Mateusz-alicante/Praxis3-PB/1. Design Process Artifacts/Pictures/Prototyping/Initial_Box_Design.webp

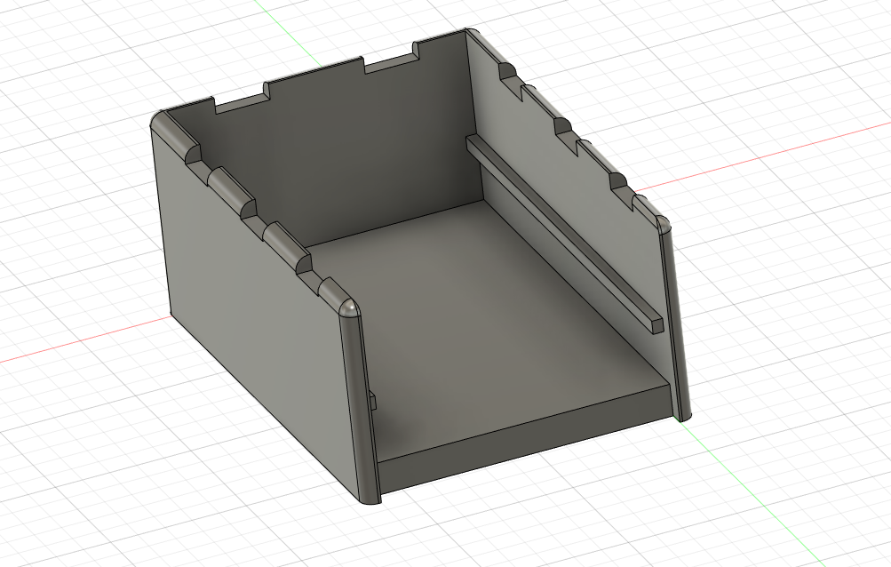
1. Design Process Artifacts/Pictures/Prototyping/Initial_Box_Design.webp
