Mateusz-alicante/Praxis3-PB/1. Design Process Artifacts/Pictures/Prototyping/Initial_Button_CAD.png

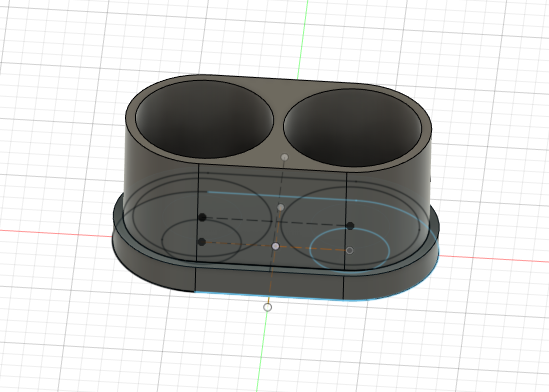
1. Design Process Artifacts/Pictures/Prototyping/Initial_Button_CAD.png
