Mateusz-alicante/Praxis3-PB/1. Design Process Artifacts/Pictures/Prototyping/Initial_Circuit_Diagram.webp

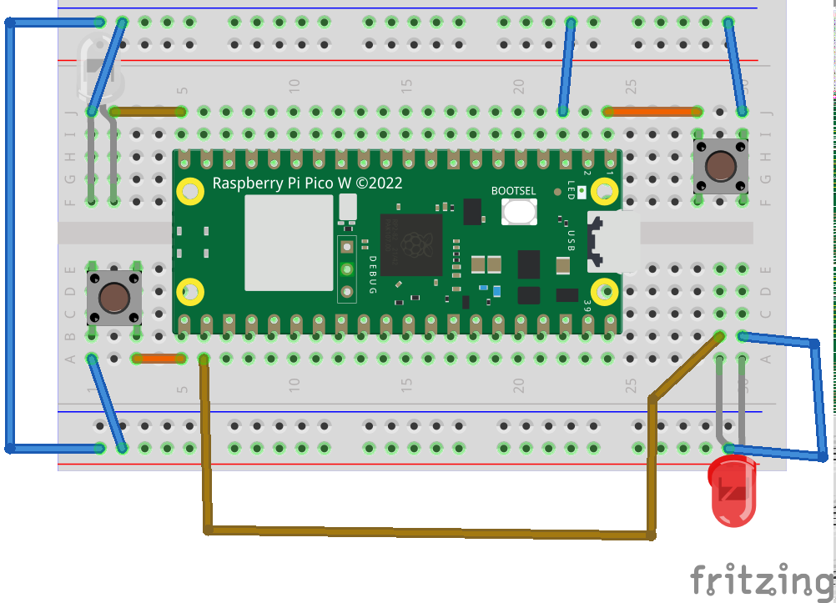
1. Design Process Artifacts/Pictures/Prototyping/Initial_Circuit_Diagram.webp
