Mateusz-alicante/Praxis3-PB/1. Design Process Artifacts/Pictures/Prototyping/Initial_Integration_Idea.webp

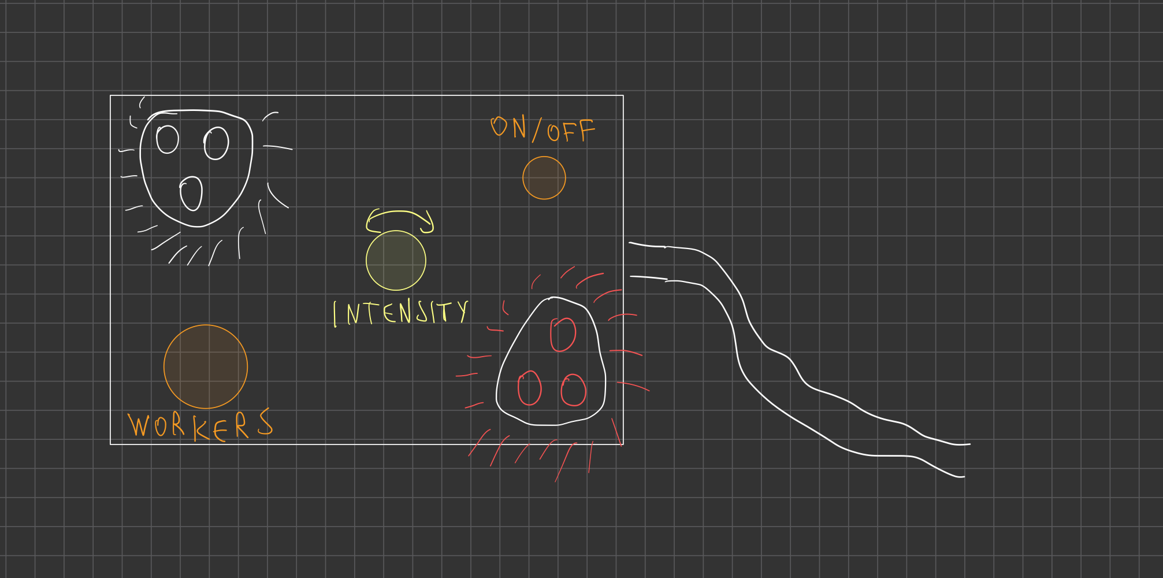
1. Design Process Artifacts/Pictures/Prototyping/Initial_Integration_Idea.webp
