Mateusz-alicante/Praxis3-PB/2. Final Design Artifacts/Final_CAD_CAM/Pictures/Section_View_2.png

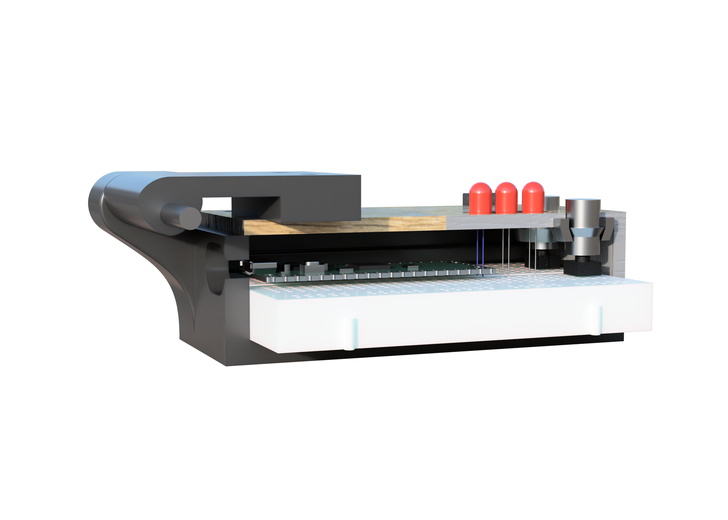
2. Final Design Artifacts/Final_CAD_CAM/Pictures/Section_View_2.png
