Mateusz-alicante/Praxis3-PB/2. Final Design Artifacts/Final_Hardware/Final_Circuit_Diagram.png

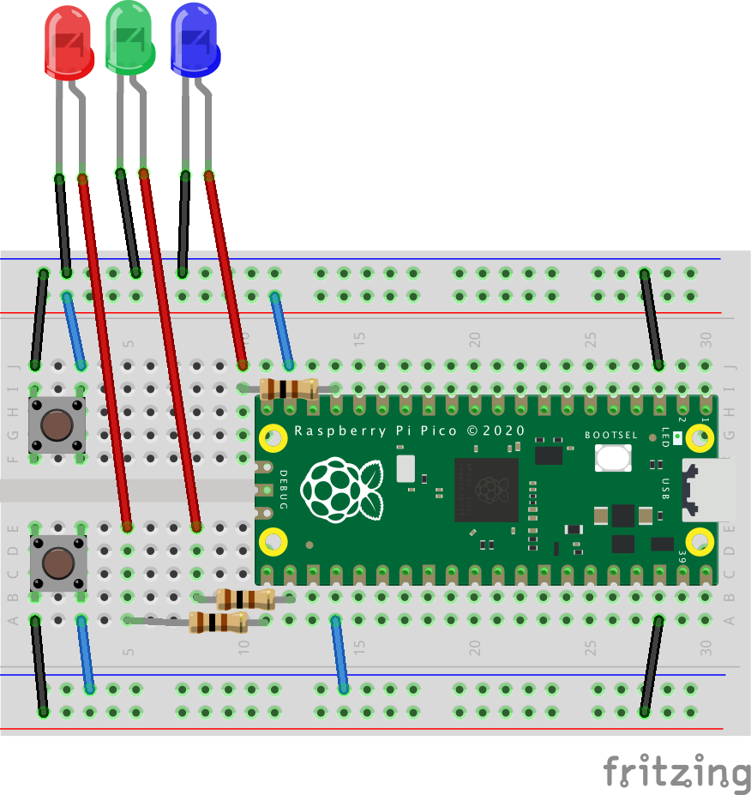
2. Final Design Artifacts/Final_Hardware/Final_Circuit_Diagram.png
