Mateusz-alicante/Praxis3-PB/2. Final Design Artifacts/Final_Software/State_Diagram.png

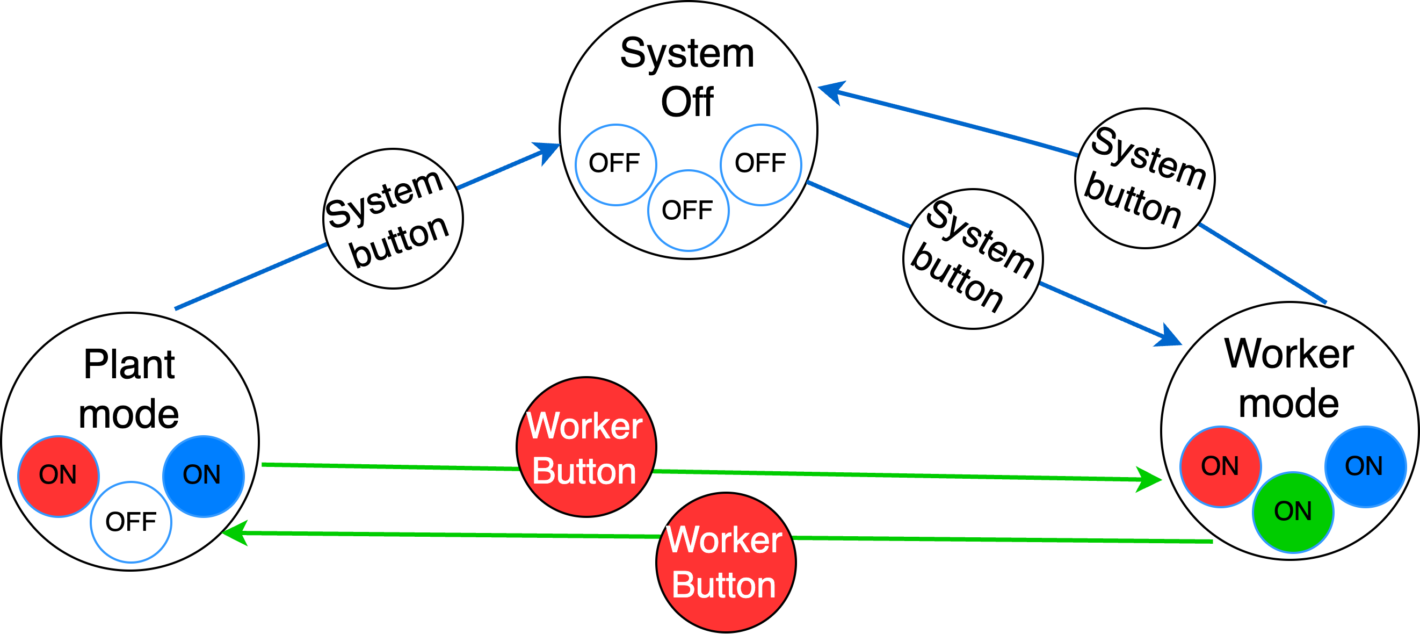
2. Final Design Artifacts/Final_Software/State_Diagram.png
