Mateusz-alicante/Praxis3-PB/2. Final Design Artifacts/Key_Design_Decisions/Software_Decisions.png

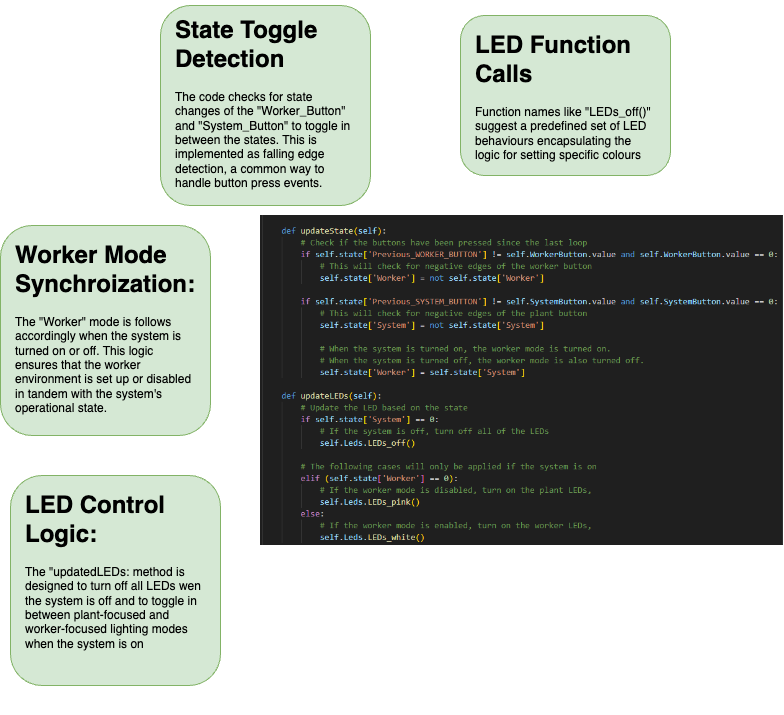
2. Final Design Artifacts/Key_Design_Decisions/Software_Decisions.png
