Mateusz-alicante/Praxis3-PB/README.png

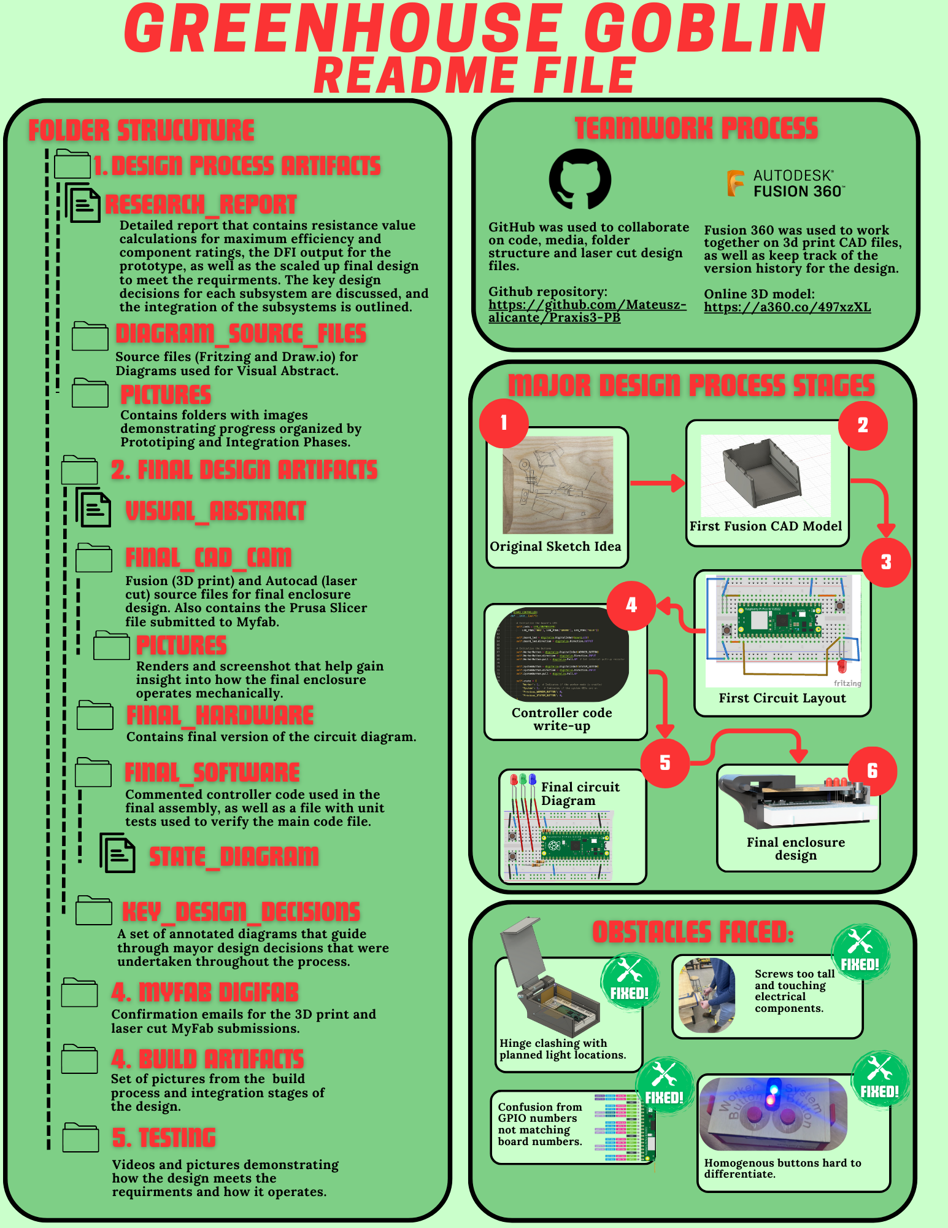
README.png
