Mateusz-alicante/Praxis3-PB/1. Design Process Artifacts/Pictures/Integration/4.Hole_Locations_For_Button_Cut_Based_On_Assembly.png

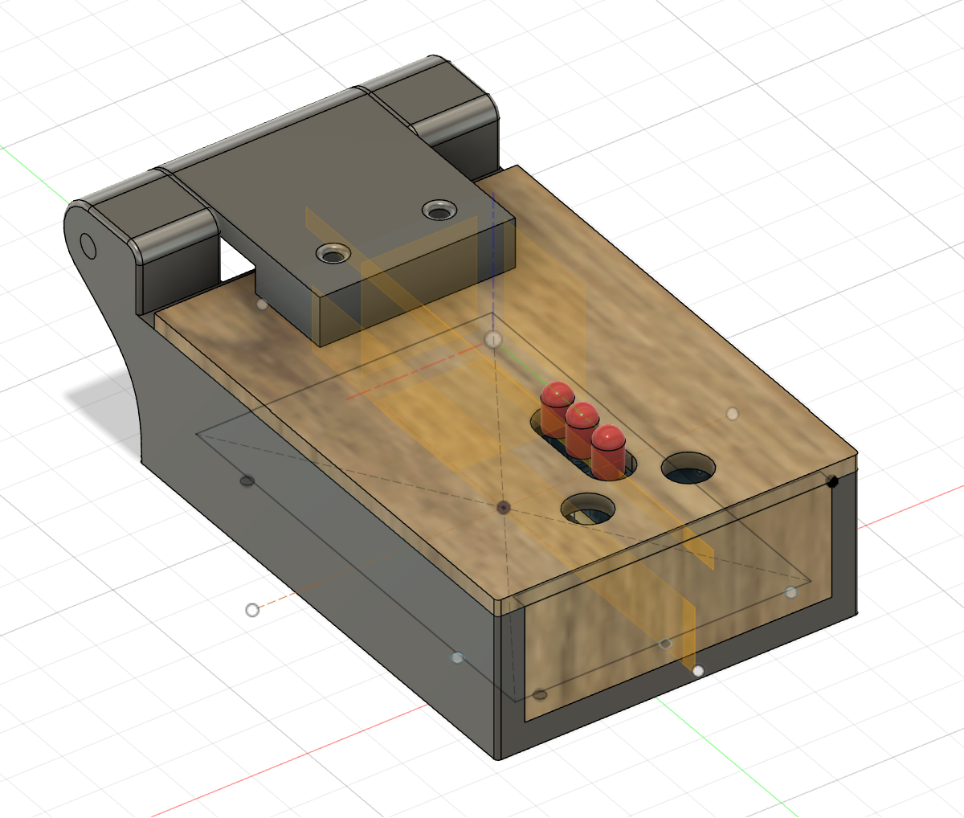
1. Design Process Artifacts/Pictures/Integration/4.Hole_Locations_For_Button_Cut_Based_On_Assembly.png
