Mateusz-alicante/Praxis3-PB/1. Design Process Artifacts/Pictures/Integration/5.3D_Print_Time_Check.webp

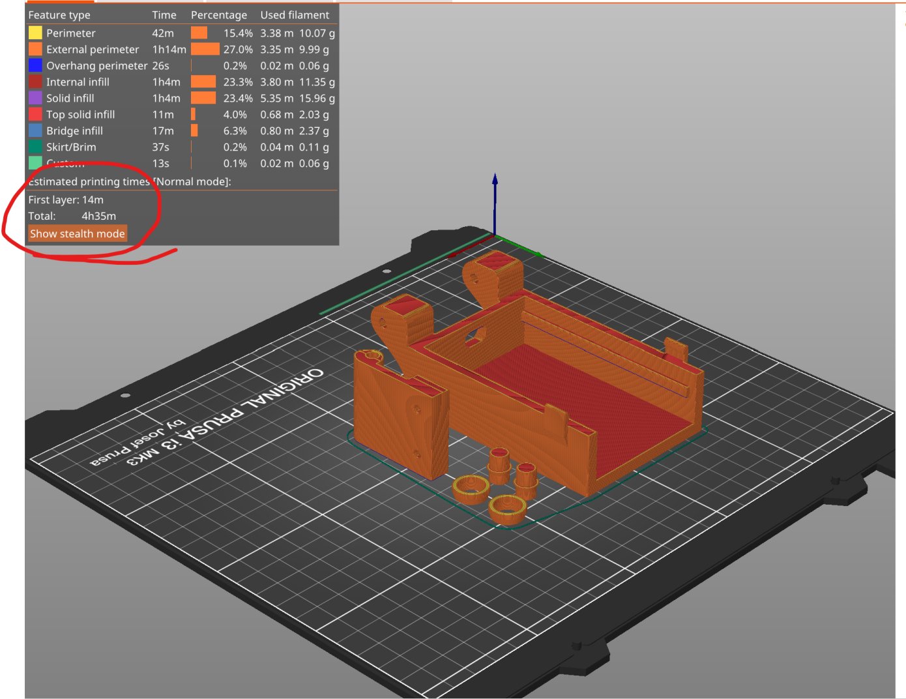
1. Design Process Artifacts/Pictures/Integration/5.3D_Print_Time_Check.webp
