Mateusz-alicante/Praxis3-PB/2. Final Design Artifacts/Final_CAD_CAM/Final_3D_Print.png

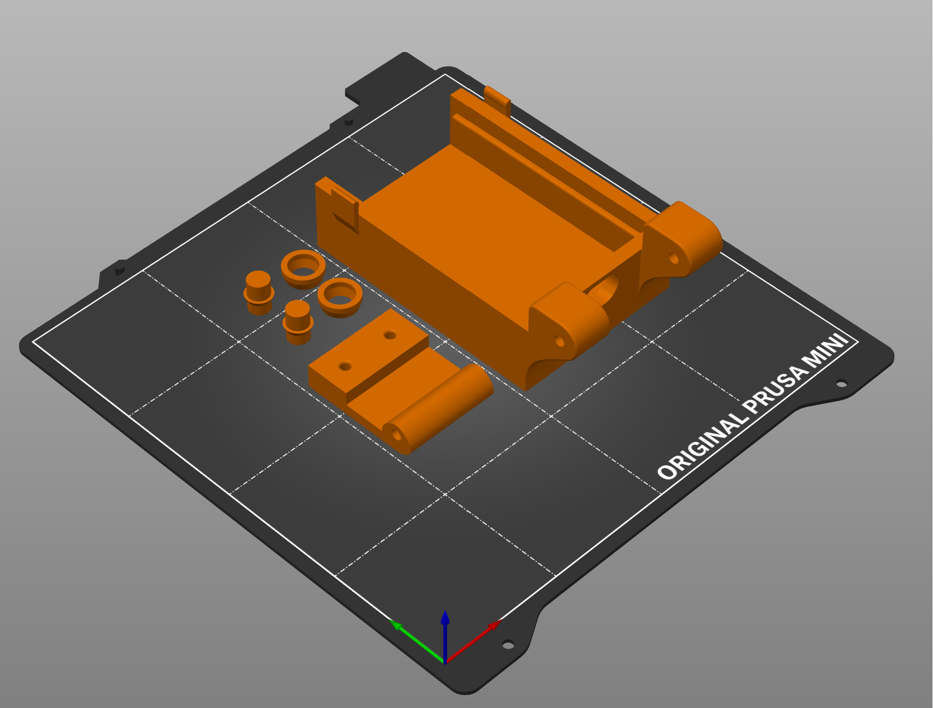
2. Final Design Artifacts/Final_CAD_CAM/Final_3D_Print.png
