Mateusz-alicante/Praxis3-PB/2. Final Design Artifacts/Final_CAD_CAM/Pictures/Assembly_Cross_Section.webp

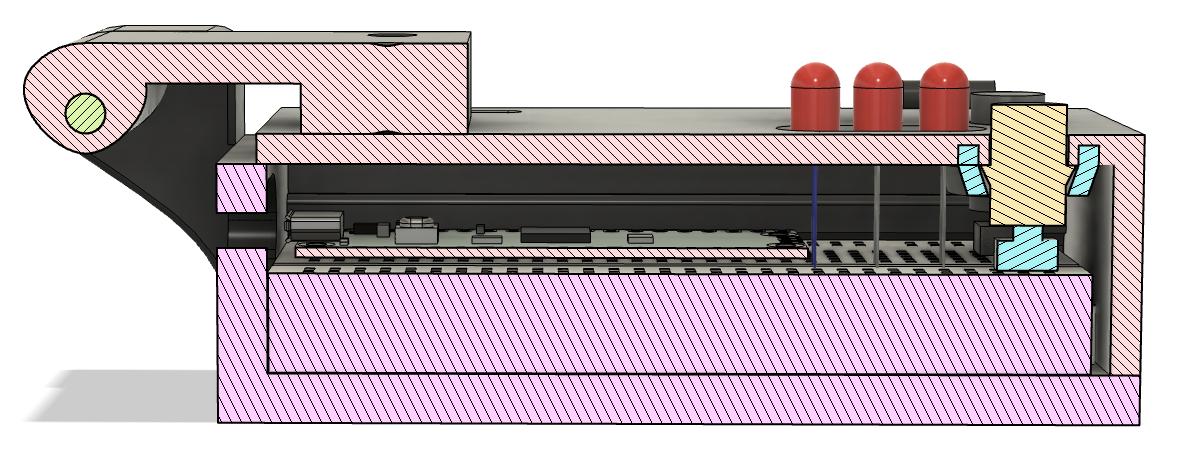
2. Final Design Artifacts/Final_CAD_CAM/Pictures/Assembly_Cross_Section.webp
