Mateusz-alicante/Praxis3-PB/2. Final Design Artifacts/Final_CAD_CAM/Pictures/Front_Assembly_Render.webp

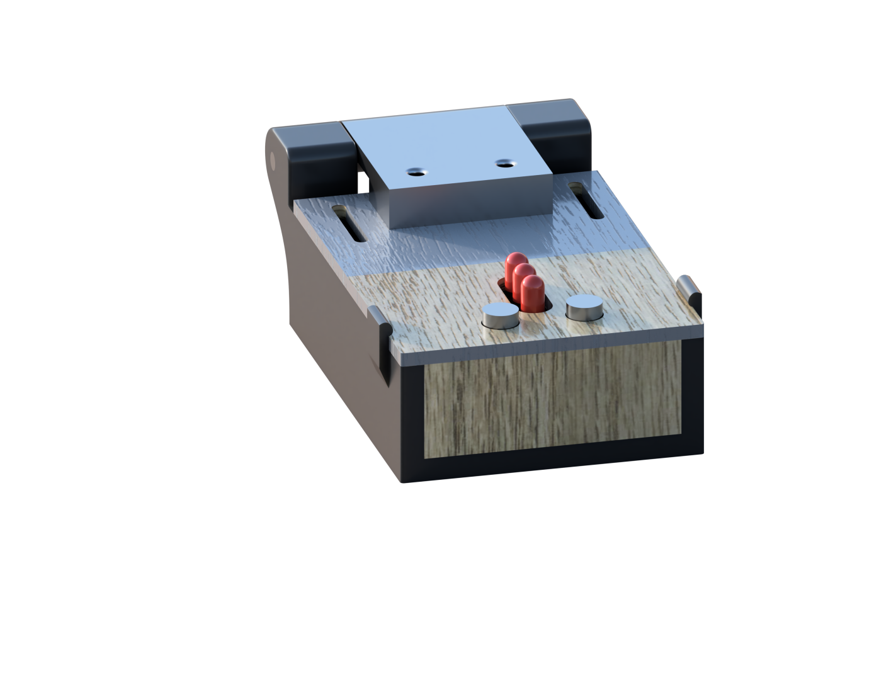
2. Final Design Artifacts/Final_CAD_CAM/Pictures/Front_Assembly_Render.webp
