Mateusz-alicante/Praxis3-PB/4. Build Artifacts/Assembling_Final_Circuit.webp

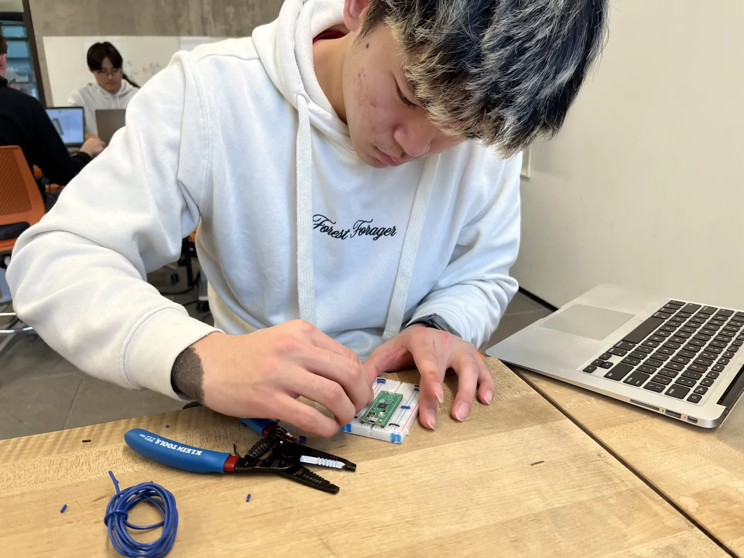
4. Build Artifacts/Assembling_Final_Circuit.webp
