Mateusz-alicante/Praxis3-PB/4. Build Artifacts/CircuitPython_Final_Code_Upload.webp

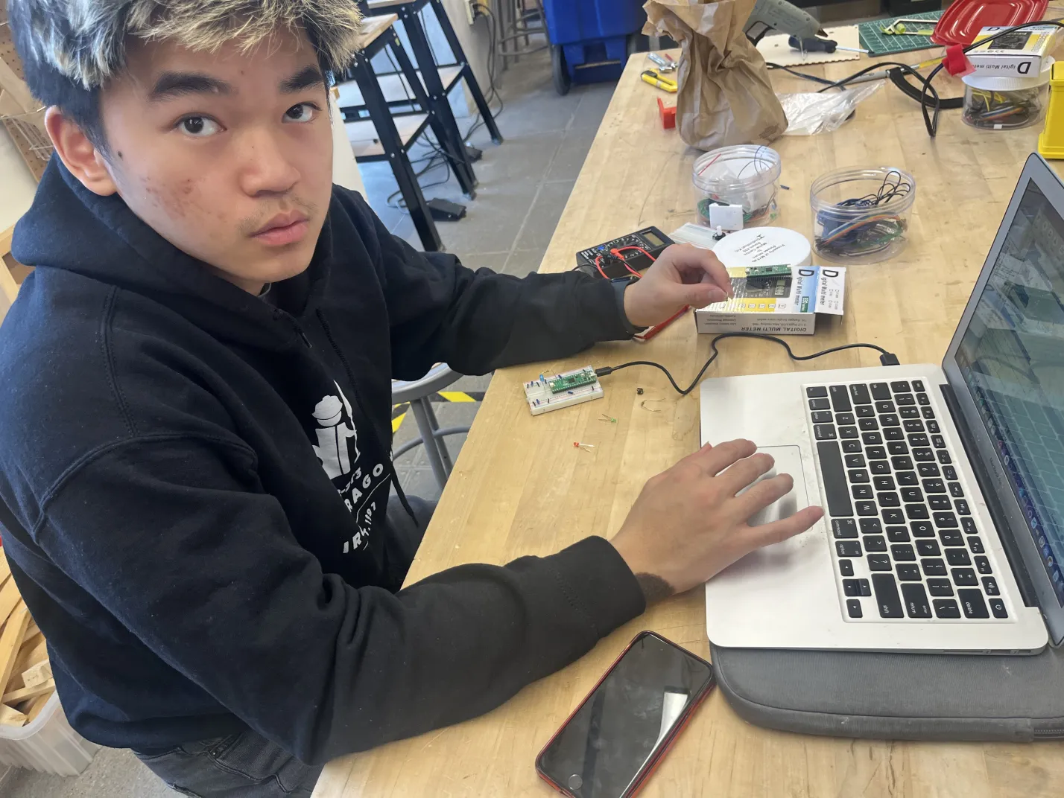
4. Build Artifacts/CircuitPython_Final_Code_Upload.webp
