Mateusz-alicante/Praxis3-PB/4. Build Artifacts/Enclosure_3D_Print_Collection.webp

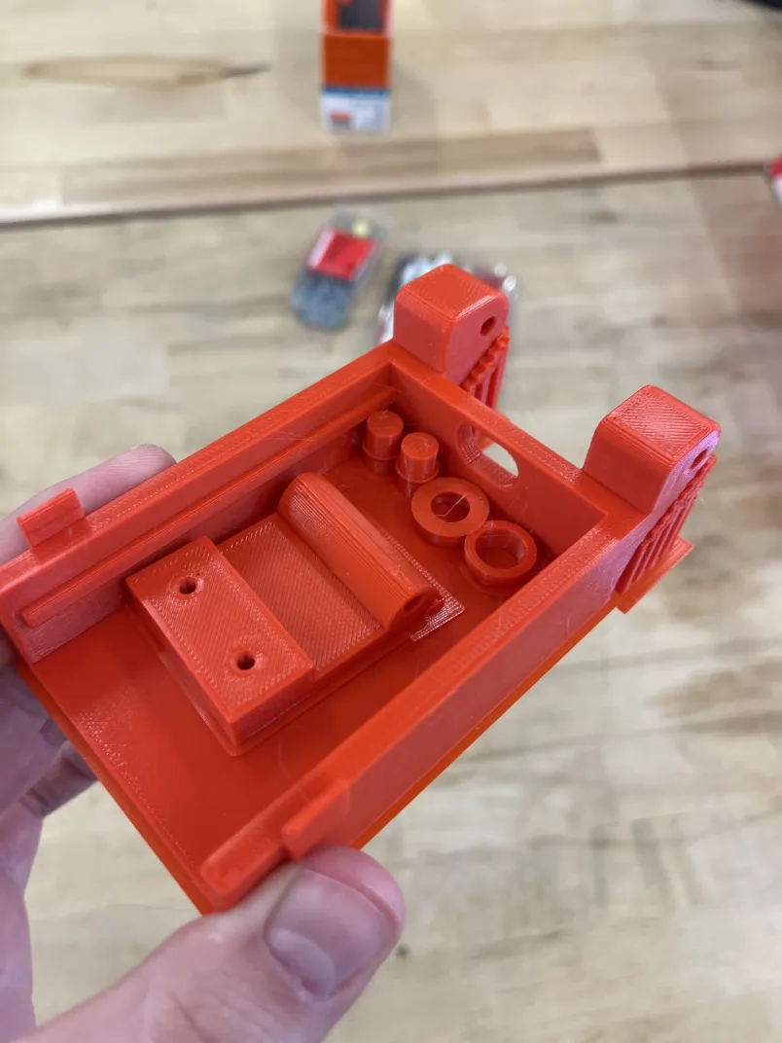
4. Build Artifacts/Enclosure_3D_Print_Collection.webp
