Mateusz-alicante/Praxis3-PB/4. Build Artifacts/Enclosure_Assembly_Without_Electrical_Components.webp

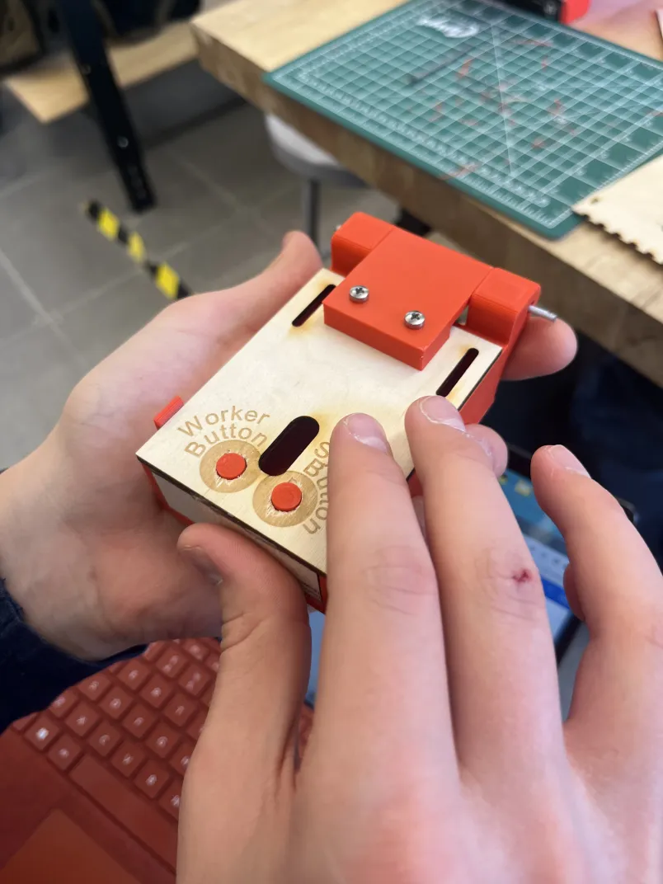
4. Build Artifacts/Enclosure_Assembly_Without_Electrical_Components.webp
