Mateusz-alicante/Praxis3-PB/4. Build Artifacts/Final_Circuit.png

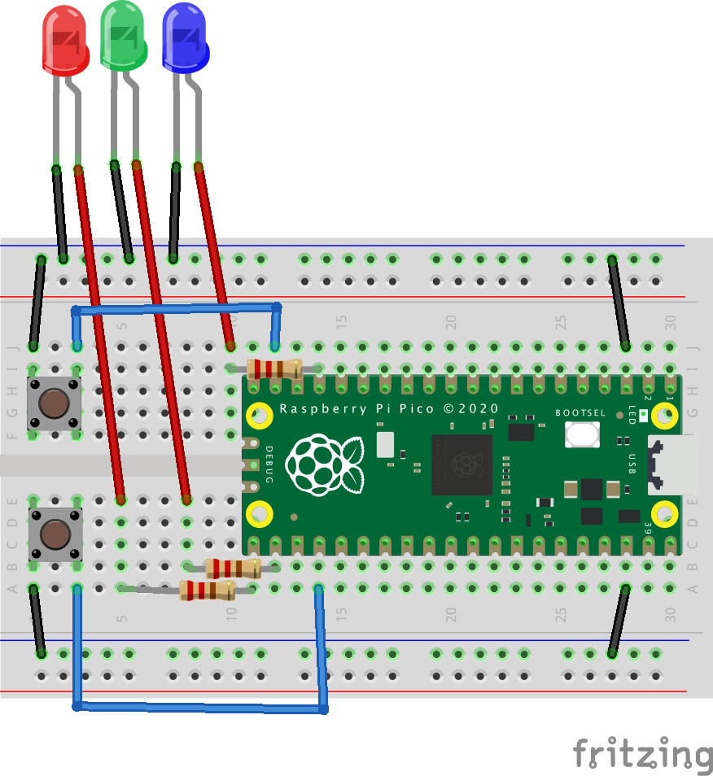
4. Build Artifacts/Final_Circuit.png
