Mateusz-alicante/Praxis3-PB/4. Build Artifacts/Screws_Touched_Raspberry_Pi_So_Shortening_Them.webp

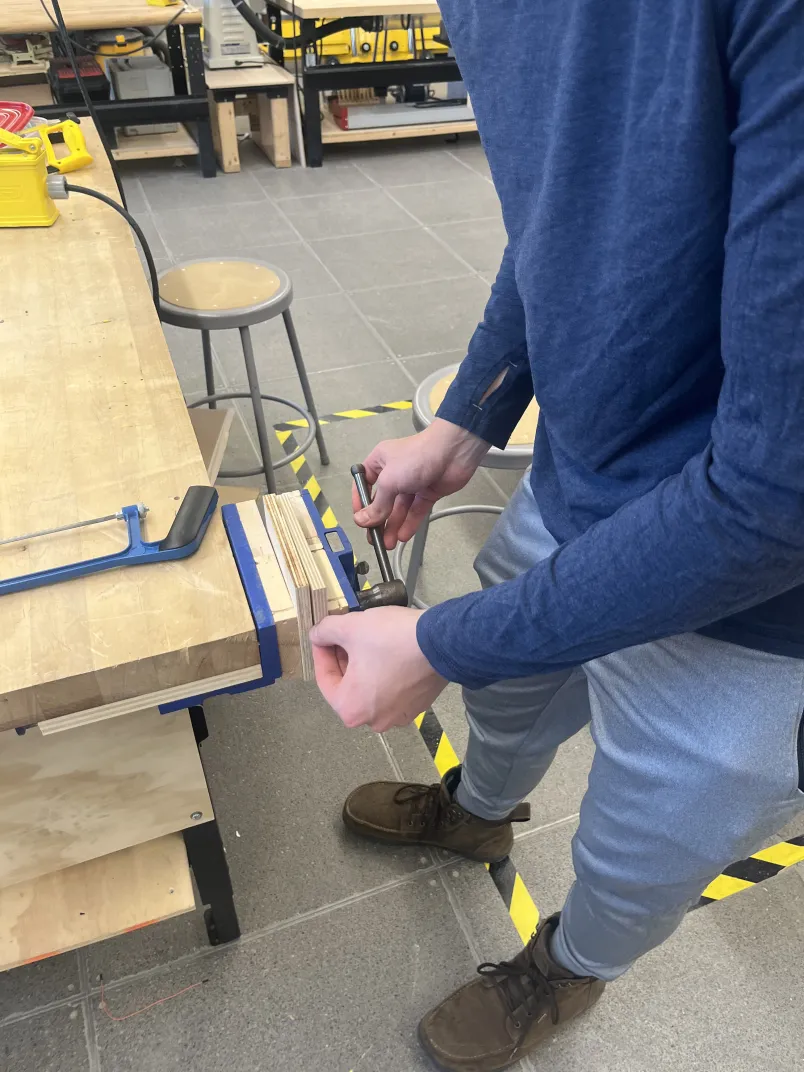
4. Build Artifacts/Screws_Touched_Raspberry_Pi_So_Shortening_Them.webp
