Mateusz-alicante/Praxis3-PB/4. Build Artifacts/Temporary_Hinge.webp

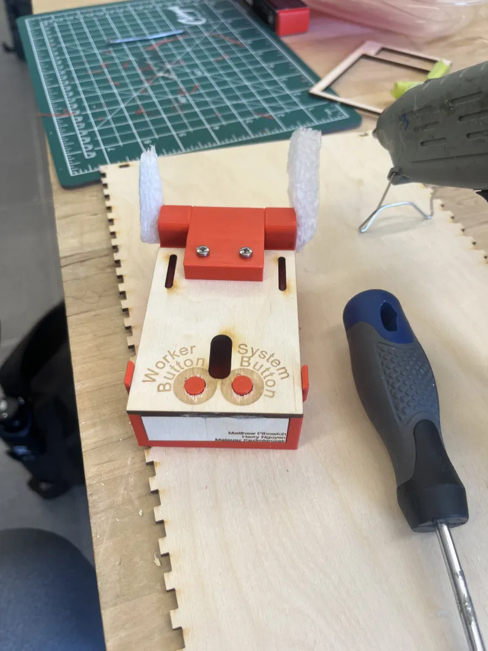
4. Build Artifacts/Temporary_Hinge.webp
