Mateusz-alicante/Praxis3-PB/5. Testing/Plant_Mode_Final_LED_Test.webp

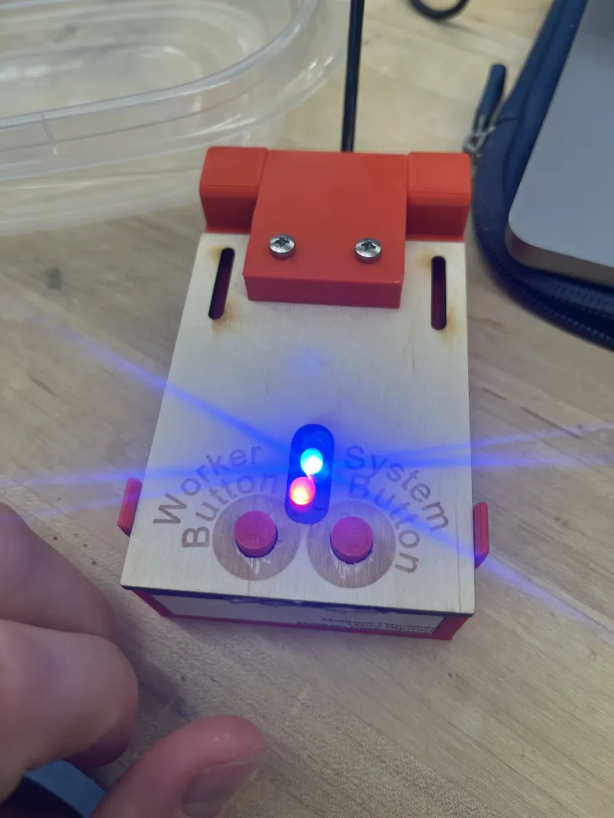
5. Testing/Plant_Mode_Final_LED_Test.webp
