Mateusz-alicante/Praxis3-PB/5. Testing/Testing_Brightness_And_White_Color_At_Distance.jpg

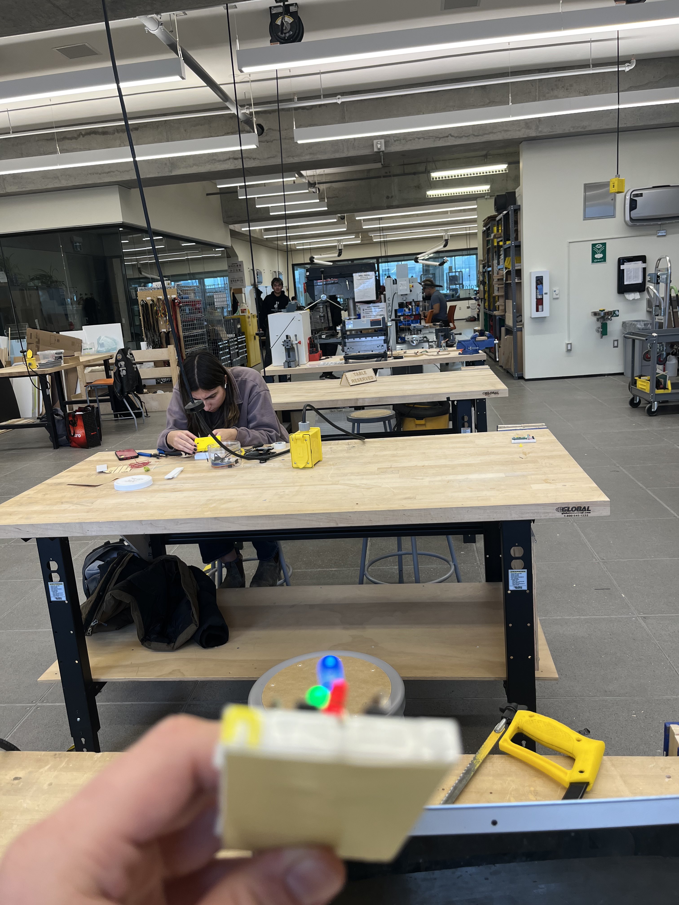
5. Testing/Testing_Brightness_And_White_Color_At_Distance.jpg
